Romanhery/PlaiKeeb/Case/3d-Models/Cherry-MX.STEP

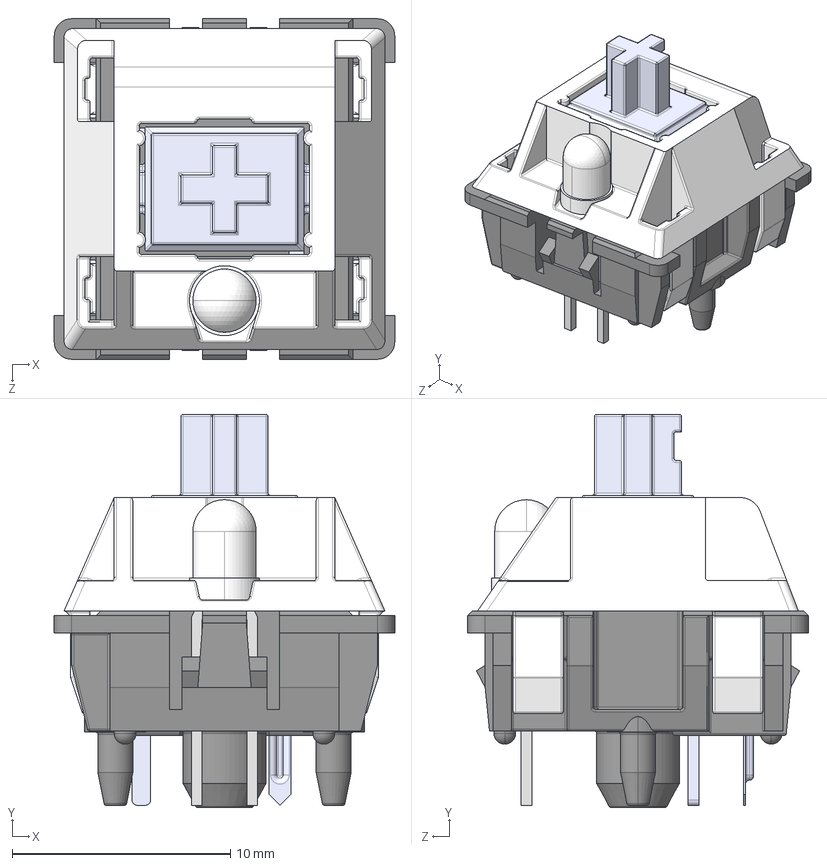
[picture p21: CAD file, 2026-08-08]
Case/3d-Models/Cherry-MX.STEP
15.6 x 18.0 x 15.6 mm
Bottom
Pulsador
Top
Pieza5^Cherry MX
Pin1
Pin2
Led 3mm_trans
