Romanhery/PlaiKeeb/Case/3d-Models/EC11_Rotary_Encoder_Switched.step

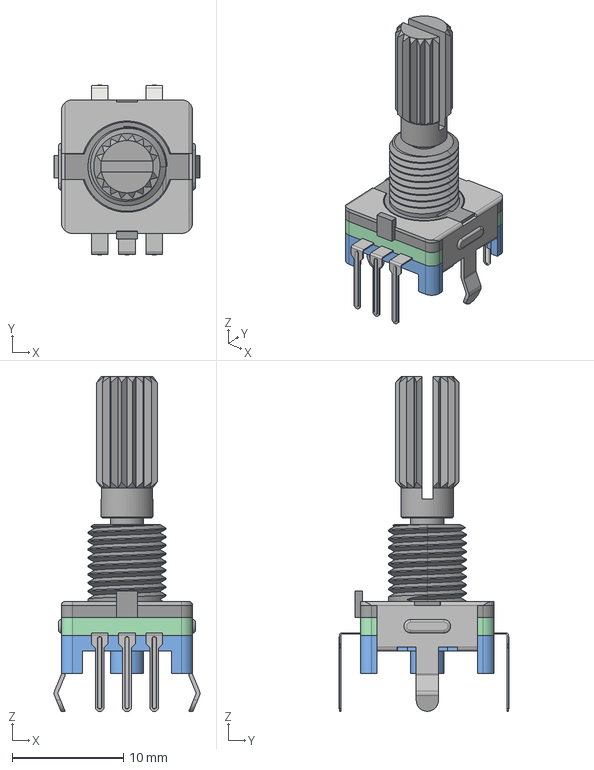
[picture p22: CAD file, 2026-08-08]
Case/3d-Models/EC11_Rotary_Encoder_Switched.step
13.1 x 15.3 x 30.1 mm
